WKossmann/Panda-Bamboo/20170629_163319.jpg

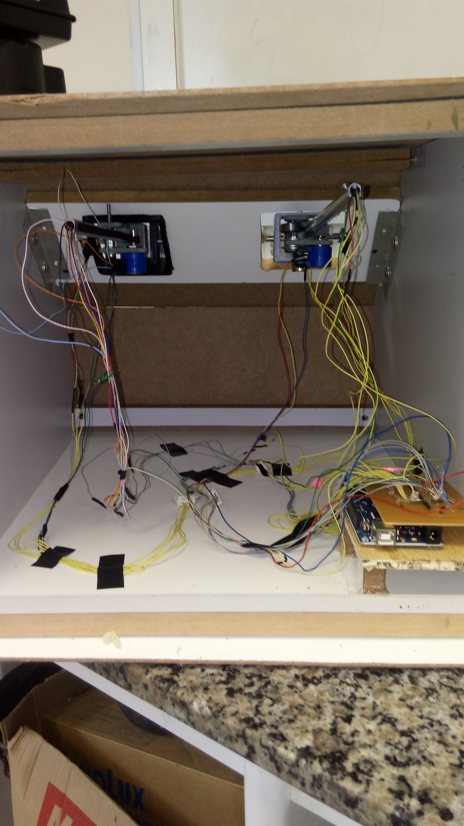
20170629_163319.jpg
