WKossmann/Panda-Bamboo/20170629_171724.jpg

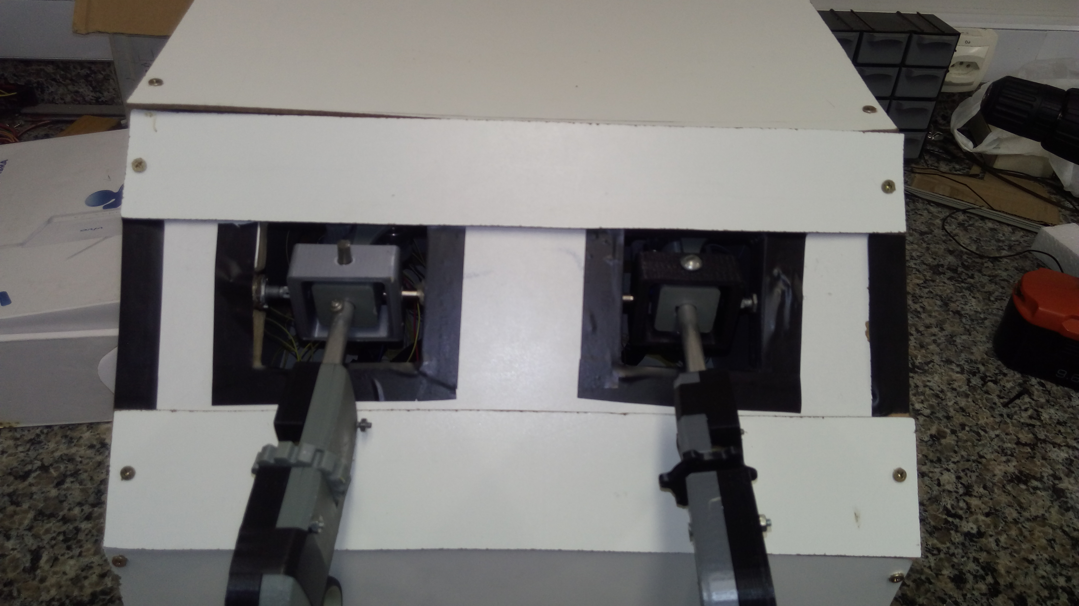
20170629_171724.jpg
