WKossmann/Panda-Bamboo/IMG_20170504_185945.jpg

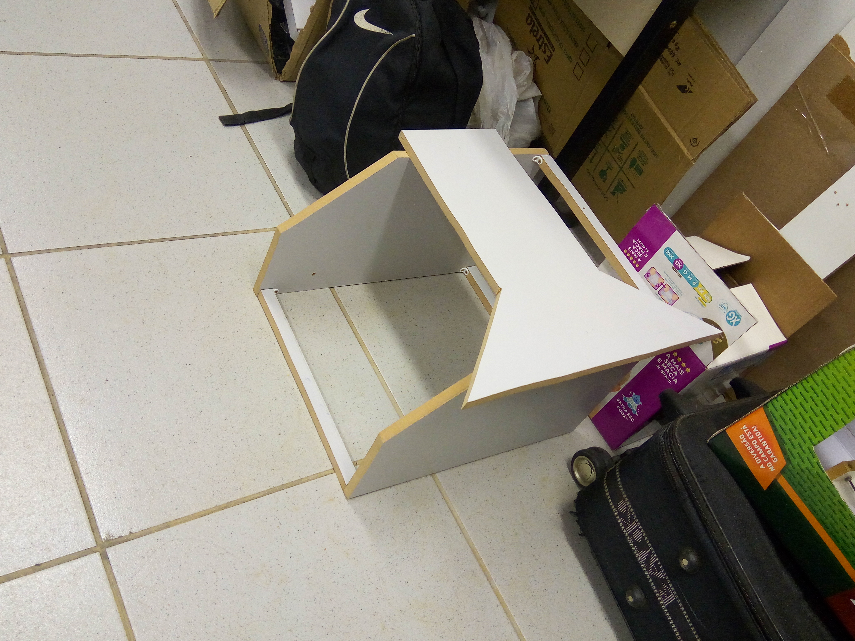
IMG_20170504_185945.jpg
