WKossmann/Panda-Bamboo/IMG_20170504_185959.jpg

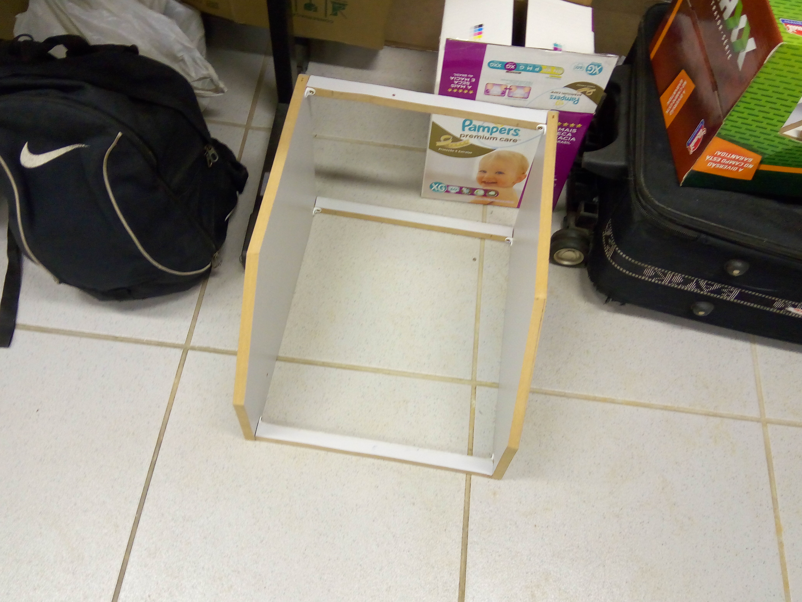
IMG_20170504_185959.jpg
